larry-athey/climate-czar/Diagrams/Cimate-Czar-Server-Mobile-UI.jpg

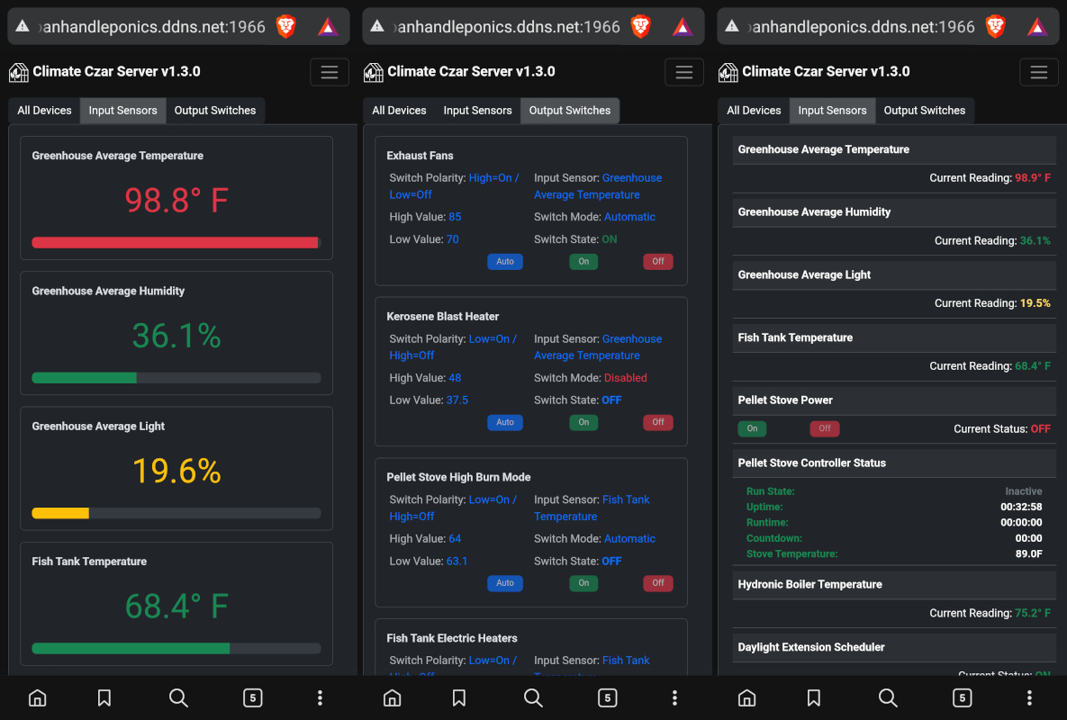
Diagrams/Cimate-Czar-Server-Mobile-UI.jpg
